Pasta38/SQM_PS/Photos/20221105_104228.jpg

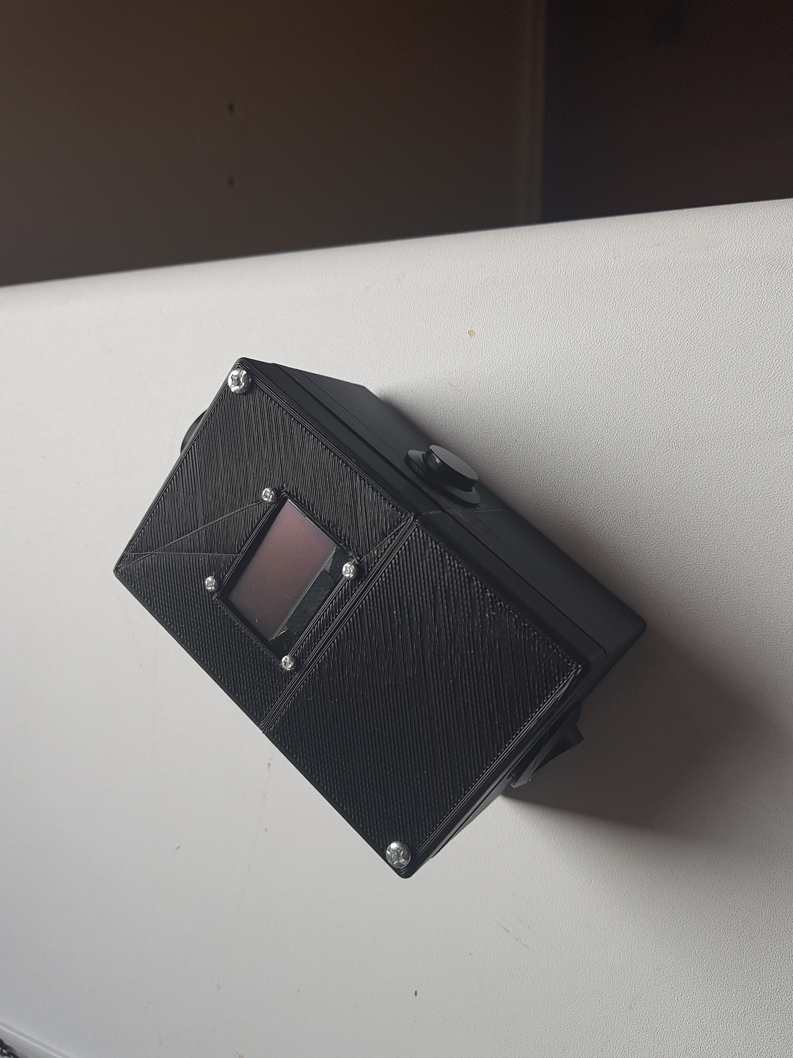
Photos/20221105_104228.jpg
