Pasta38/SQM_PS/Photos/20221105_104556.jpg

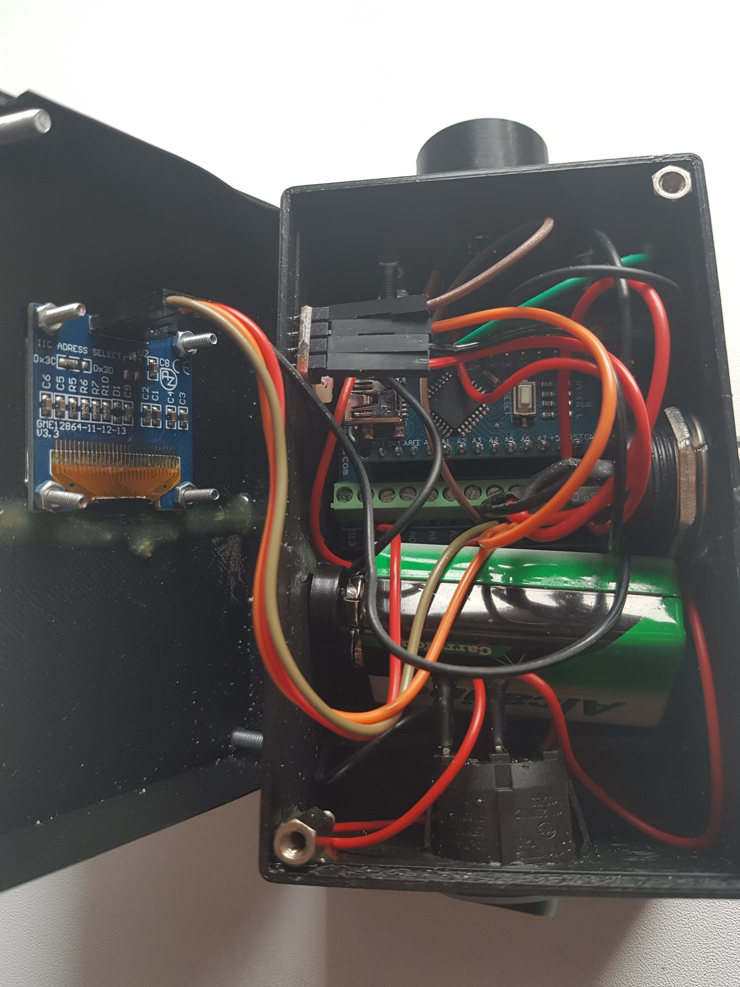
Photos/20221105_104556.jpg
